padeler/bitbox/bitbox/tetris.h

int8_t I0[] = { 1,     0,0 };
int8_t I1[] = { 4,     0,0, 1,0, 2,0, 3,0};

int8_t *I_masks[2] = { I0, I1 } 

//int8_t L0[][] = { {0, 0}, {1,0} };
//int8_t L1[][] = { {0, 0}, {1,0}, {2,0} };
//int8_t L2[][] = { {0, 0}, {1,-1}, {2,-1} };
//int8_t L3[][] = { {0, 0}, {1,2} };
//
//int8_t J0[][] = { {0, 0}, {1,0} };
//int8_t J1[][] = { {0, 0}, {1,0}, {2,0} };
//int8_t J2[][] = { {0, 0}, {1,-1}, {2,-1} };
//int8_t J3[][] = { {0, 0}, {1,2} };
//
//
//
//class Tetris
//{
//  Tetris(){}
//
//
//  void spin_once();
//
//  // create a random new block 
//  // and find its destination
//  void new_block(); 
//
//  // check is there is one or more full lines and delete them.
//  void delete_full_lines();
//
//private:
//  Point dst;
//  uint8_t block;
//  Point block_pos;  
//}
